solarmon/RGBtoHDMI/CPLD/RGBtoHDMI Amiga Denise DIP CPLD Rev 1.1/RGBtoHDMI Amiga Denise DIP CPLD  Rev 1.1 - Top Angle with Pi.png

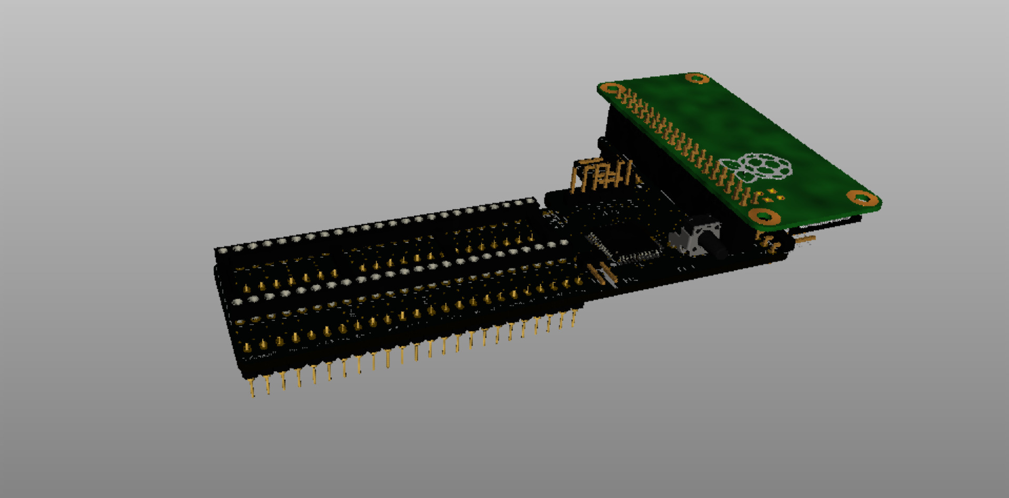
CPLD/RGBtoHDMI Amiga Denise DIP CPLD Rev 1.1/RGBtoHDMI Amiga Denise DIP CPLD Rev 1.1 - Top Angle with Pi.png
