solarmon/RGBtoHDMI/CPLD/RGBtoHDMI-CPLD-Quick-Start-Guide.png

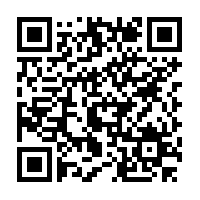
CPLD/RGBtoHDMI-CPLD-Quick-Start-Guide.png
